mhfalken/esp32_ir_gun/hw/git-images/gun-inside.jpg

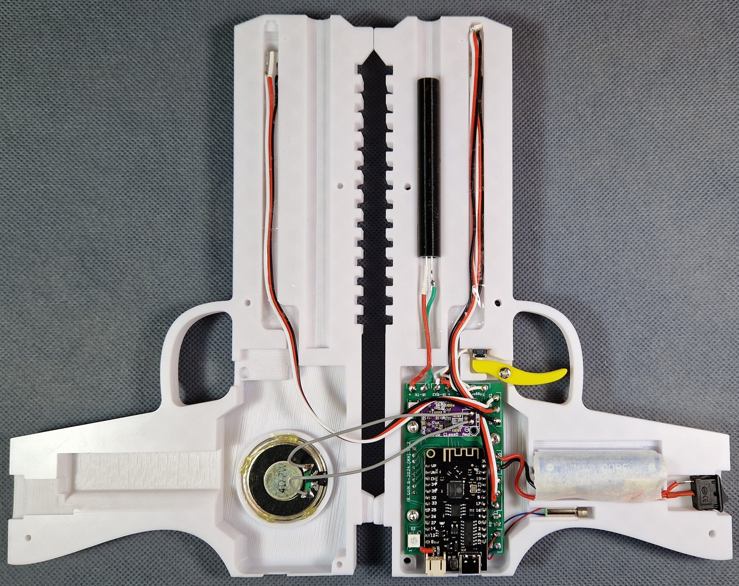
hw/git-images/gun-inside.jpg
